robinhedwards/UltimateCart/Source/QuartusProject/Max10_SD/host/synthesis/submodules/host_mm_interconnect_0_cmd_demux.sv

// (C) 2001-2015 Altera Corporation. All rights reserved.
// Your use of Altera Corporation's design tools, logic functions and other 
// software and tools, and its AMPP partner logic functions, and any output 
// files any of the foregoing (including device programming or simulation 
// files), and any associated documentation or information are expressly subject 
// to the terms and conditions of the Altera Program License Subscription 
// Agreement, Altera MegaCore Function License Agreement, or other applicable 
// license agreement, including, without limitation, that your use is for the 
// sole purpose of programming logic devices manufactured by Altera and sold by 
// Altera or its authorized distributors.  Please refer to the applicable 
// agreement for further details.


// $Id: //acds/rel/14.1/ip/merlin/altera_merlin_demultiplexer/altera_merlin_demultiplexer.sv.terp#1 $
// $Revision: #1 $
// $Date: 2014/10/06 $
// $Author: swbranch $

// -------------------------------------
// Merlin Demultiplexer
//
// Asserts valid on the appropriate output
// given a one-hot channel signal.
// -------------------------------------

`timescale 1 ns / 1 ns

// ------------------------------------------
// Generation parameters:
//   output_name:         host_mm_interconnect_0_cmd_demux
//   ST_DATA_W:           100
//   ST_CHANNEL_W:        12
//   NUM_OUTPUTS:         12
//   VALID_WIDTH:         1
// ------------------------------------------

//------------------------------------------
// Message Supression Used
// QIS Warnings
// 15610 - Warning: Design contains x input pin(s) that do not drive logic
//------------------------------------------

module host_mm_interconnect_0_cmd_demux
(
    // -------------------
    // Sink
    // -------------------
    input  [1-1      : 0]   sink_valid,
    input  [100-1    : 0]   sink_data, // ST_DATA_W=100
    input  [12-1 : 0]   sink_channel, // ST_CHANNEL_W=12
    input                         sink_startofpacket,
    input                         sink_endofpacket,
    output                        sink_ready,

    // -------------------
    // Sources 
    // -------------------
    output reg                      src0_valid,
    output reg [100-1    : 0] src0_data, // ST_DATA_W=100
    output reg [12-1 : 0] src0_channel, // ST_CHANNEL_W=12
    output reg                      src0_startofpacket,
    output reg                      src0_endofpacket,
    input                           src0_ready,

    output reg                      src1_valid,
    output reg [100-1    : 0] src1_data, // ST_DATA_W=100
    output reg [12-1 : 0] src1_channel, // ST_CHANNEL_W=12
    output reg                      src1_startofpacket,
    output reg                      src1_endofpacket,
    input                           src1_ready,

    output reg                      src2_valid,
    output reg [100-1    : 0] src2_data, // ST_DATA_W=100
    output reg [12-1 : 0] src2_channel, // ST_CHANNEL_W=12
    output reg                      src2_startofpacket,
    output reg                      src2_endofpacket,
    input                           src2_ready,

    output reg                      src3_valid,
    output reg [100-1    : 0] src3_data, // ST_DATA_W=100
    output reg [12-1 : 0] src3_channel, // ST_CHANNEL_W=12
    output reg                      src3_startofpacket,
    output reg                      src3_endofpacket,
    input                           src3_ready,

    output reg                      src4_valid,
    output reg [100-1    : 0] src4_data, // ST_DATA_W=100
    output reg [12-1 : 0] src4_channel, // ST_CHANNEL_W=12
    output reg                      src4_startofpacket,
    output reg                      src4_endofpacket,
    input                           src4_ready,

    output reg                      src5_valid,
    output reg [100-1    : 0] src5_data, // ST_DATA_W=100
    output reg [12-1 : 0] src5_channel, // ST_CHANNEL_W=12
    output reg                      src5_startofpacket,
    output reg                      src5_endofpacket,
    input                           src5_ready,

    output reg                      src6_valid,
    output reg [100-1    : 0] src6_data, // ST_DATA_W=100
    output reg [12-1 : 0] src6_channel, // ST_CHANNEL_W=12
    output reg                      src6_startofpacket,
    output reg                      src6_endofpacket,
    input                           src6_ready,
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
